mavory/PicoFlip-X/Photos/20260328_102939(0).jpg

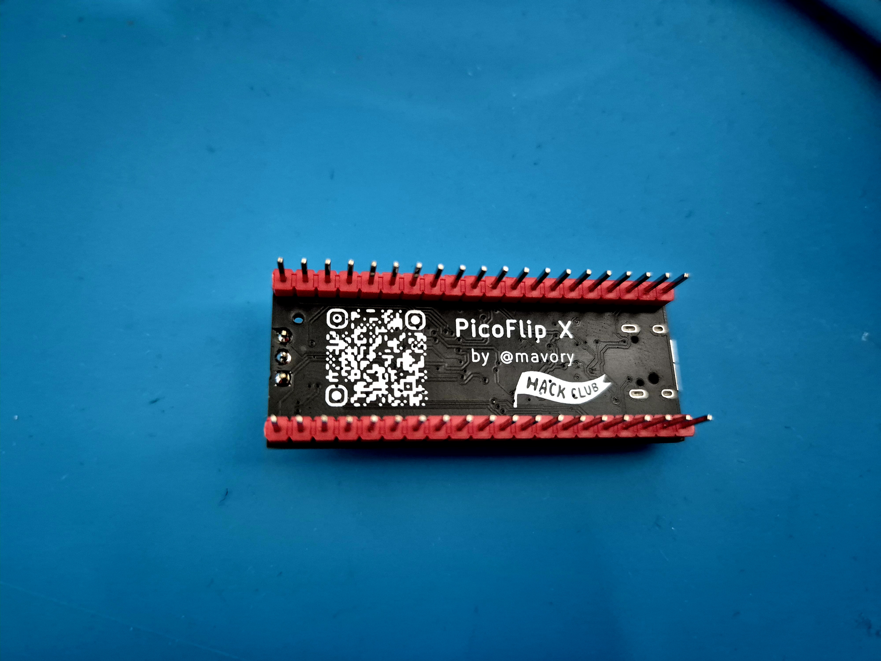
Photos/20260328_102939(0).jpg
