mavory/PicoFlip-X/Photos/20260328_102952.jpg

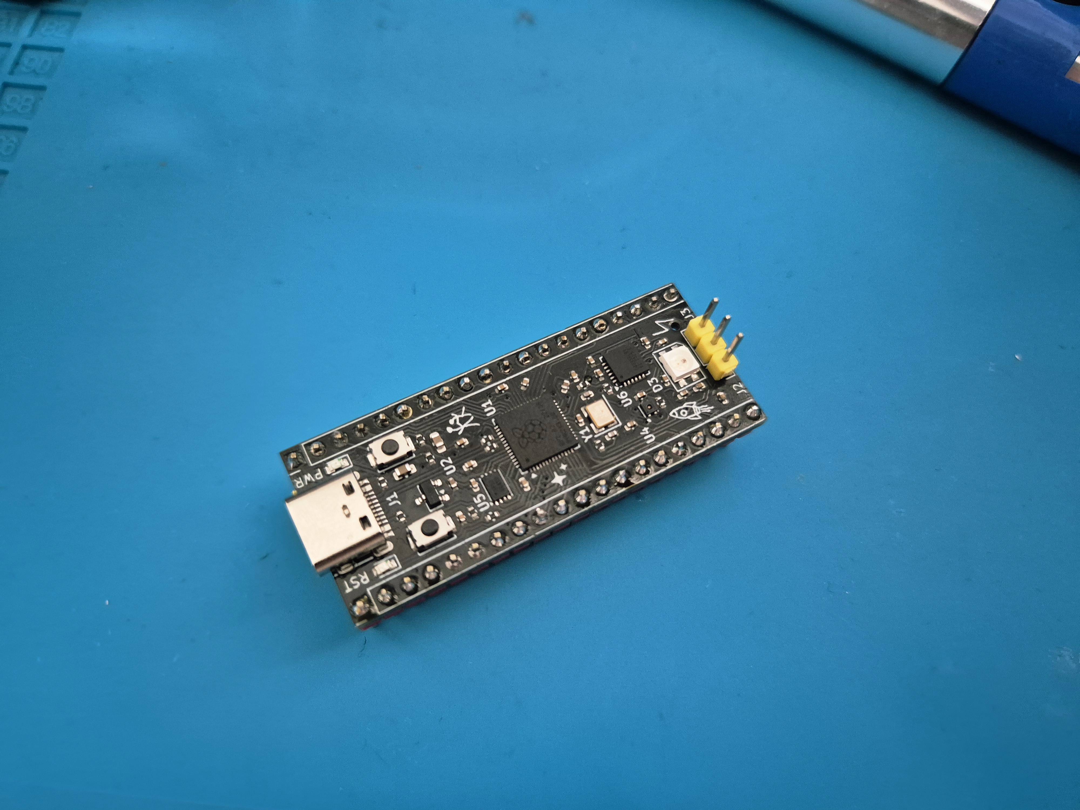
Photos/20260328_102952.jpg
