mavory/PicoFlip-X/Photos/peoples.png

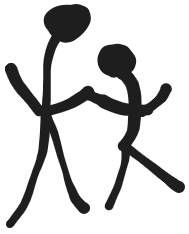
Photos/peoples.png
