mavory/PicoFlip-X/Photos/Screenshot_20260226_140506_Gallery.jpg

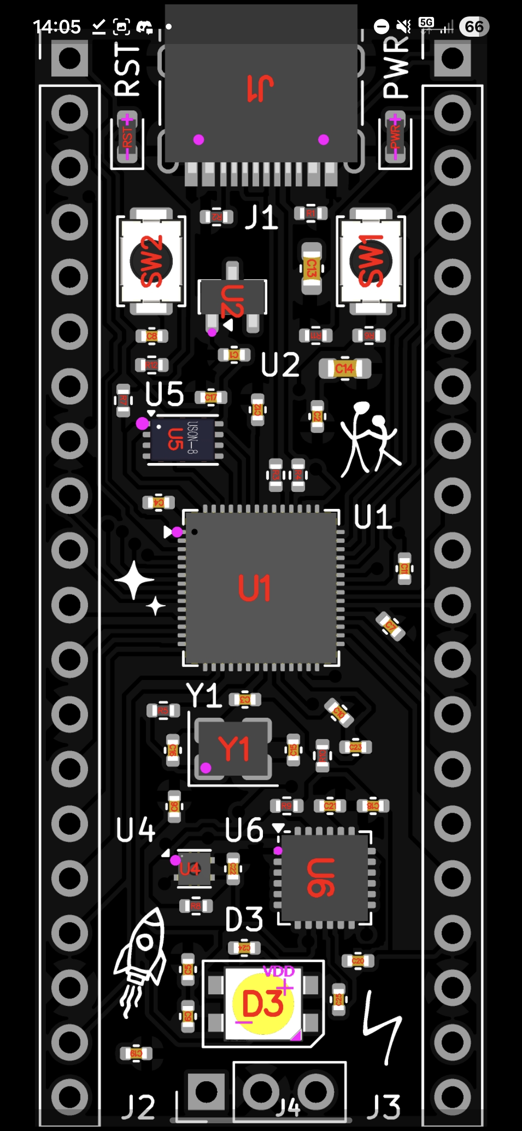
Photos/Screenshot_20260226_140506_Gallery.jpg
