mavory/PicoFlip-X/Photos/Snímek obrazovky 2026-02-14 212641.png

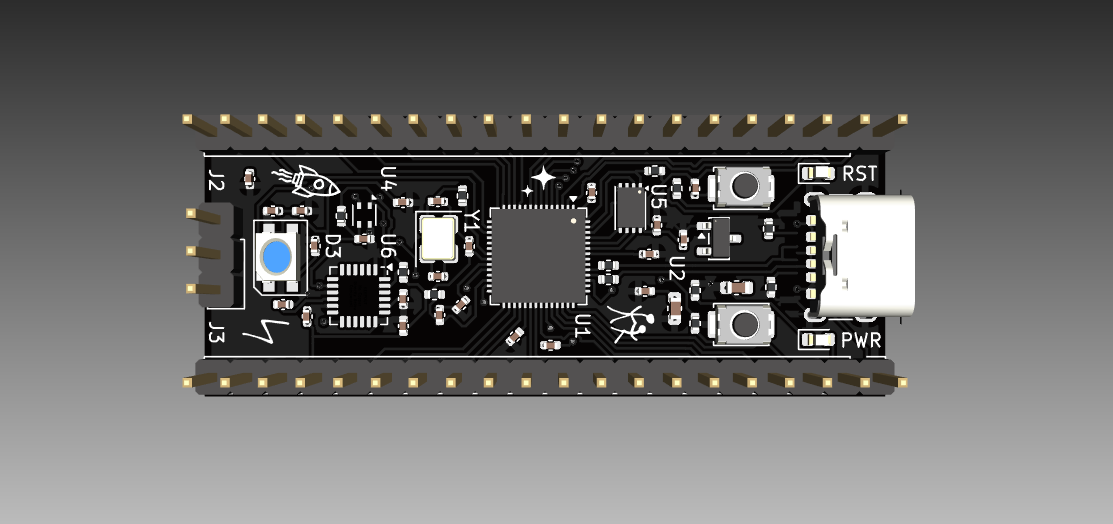
Photos/Snímek obrazovky 2026-02-14 212641.png
