mavory/PicoFlip-X/Photos/Snímek obrazovky 2026-02-14 212650.png

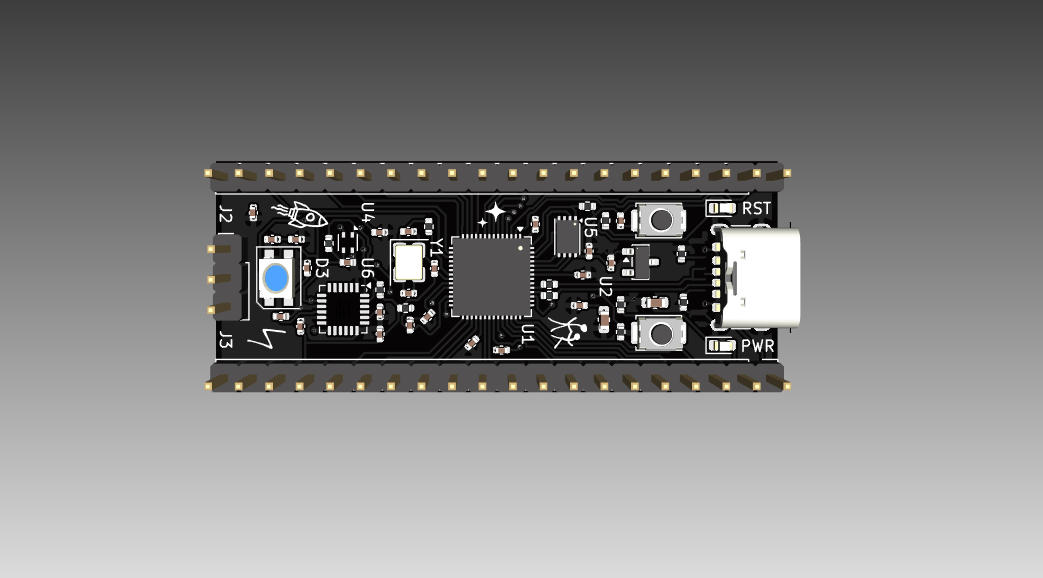
Photos/Snímek obrazovky 2026-02-14 212650.png
