mavory/PicoFlip-X/Photos/Snímek obrazovky 2026-02-14 213149.png

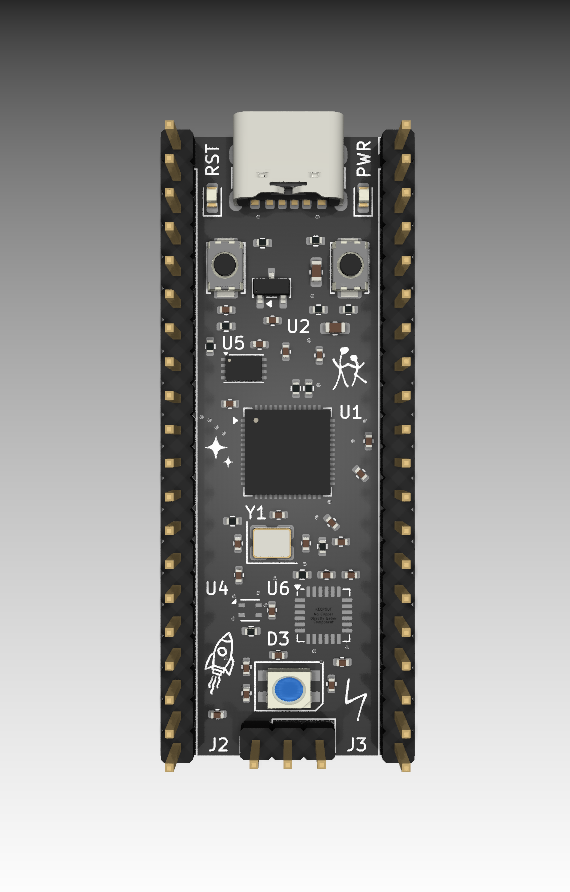
Photos/Snímek obrazovky 2026-02-14 213149.png
