mavory/PicoFlip-X/Photos/Snímek obrazovky 2026-02-14 213213.png

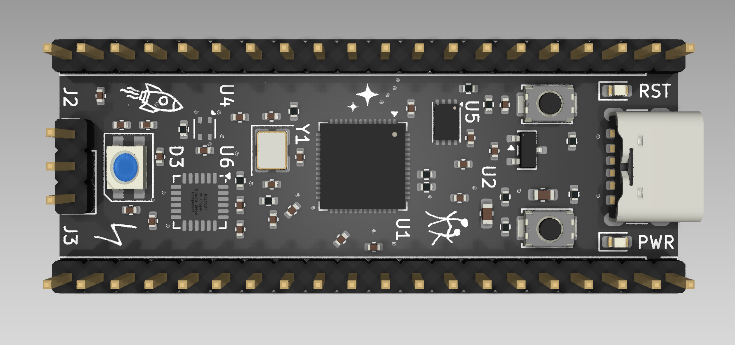
Photos/Snímek obrazovky 2026-02-14 213213.png
