mavory/PicoFlip-X/Photos/Snímek obrazovky 2026-02-14 213331.png

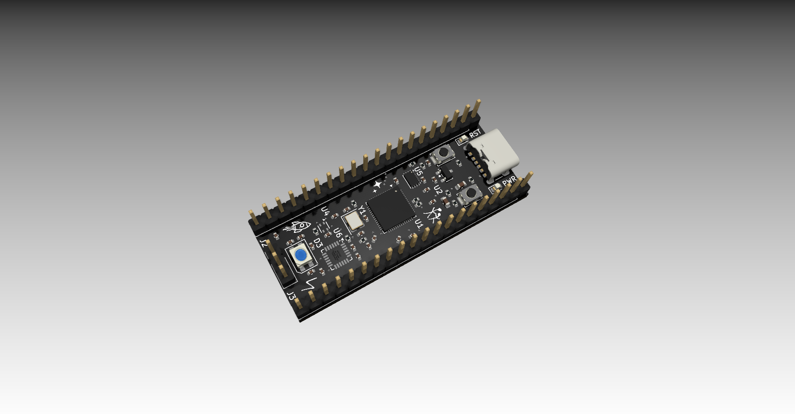
Photos/Snímek obrazovky 2026-02-14 213331.png
