mavory/PicoFlip-X/Photos/Snímek obrazovky 2026-02-15 212742.png

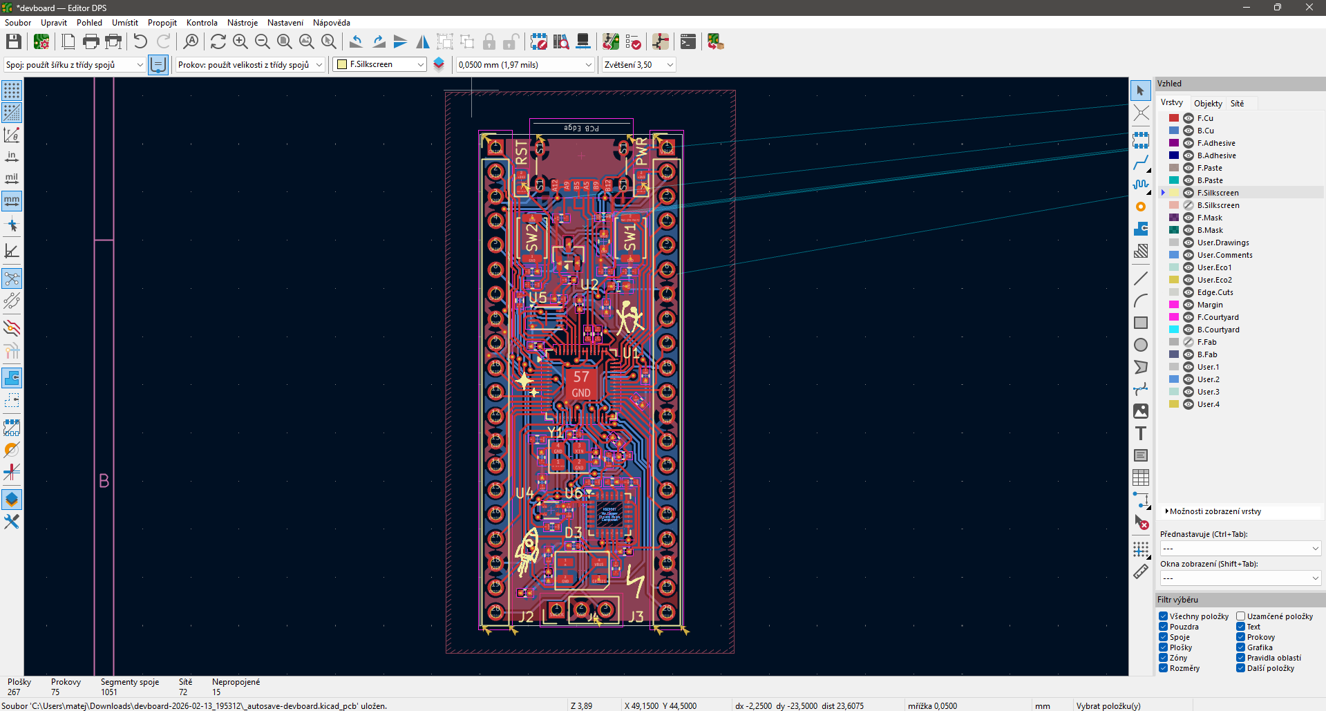
Photos/Snímek obrazovky 2026-02-15 212742.png
