mavory/PicoFlip-X/Photos/star.png

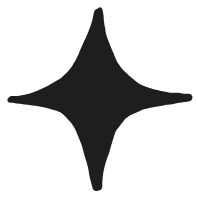
Photos/star.png
