mavory/PicoFlip-X/Photos/thunderbolt.png

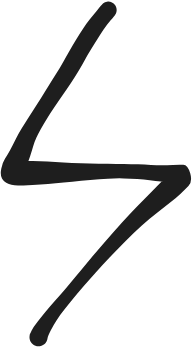
Photos/thunderbolt.png
