mavory/PicoFlip-X/Test code/20260328_125100.jpg

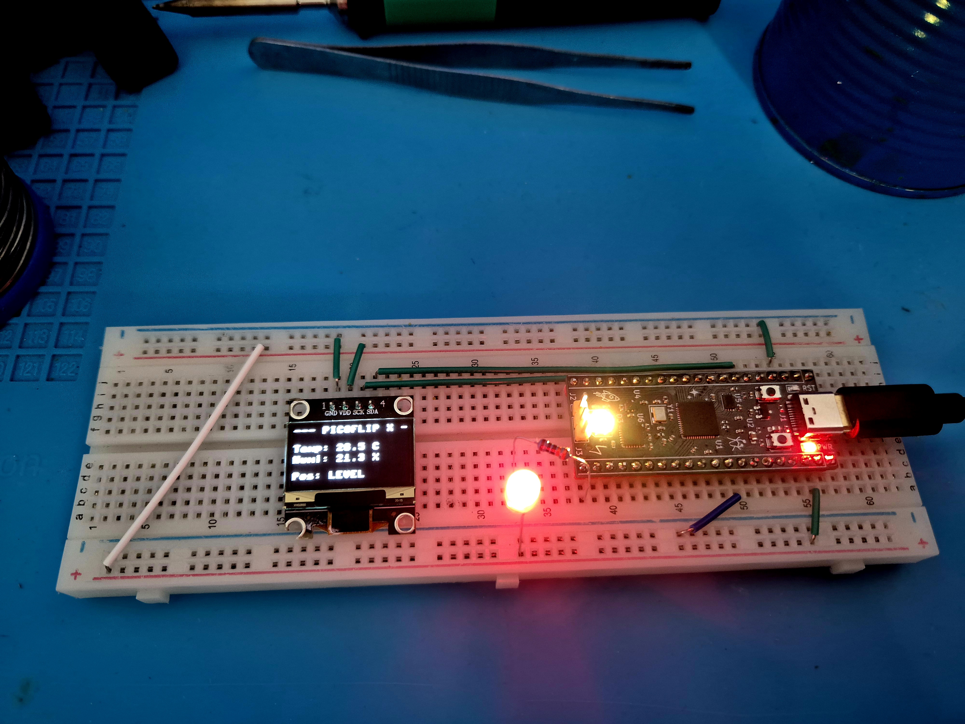
Test code/20260328_125100.jpg
